Vedatori/SleetClock/Electronics/ESP32 dev board/ESP32 dev board PCB 3D.png

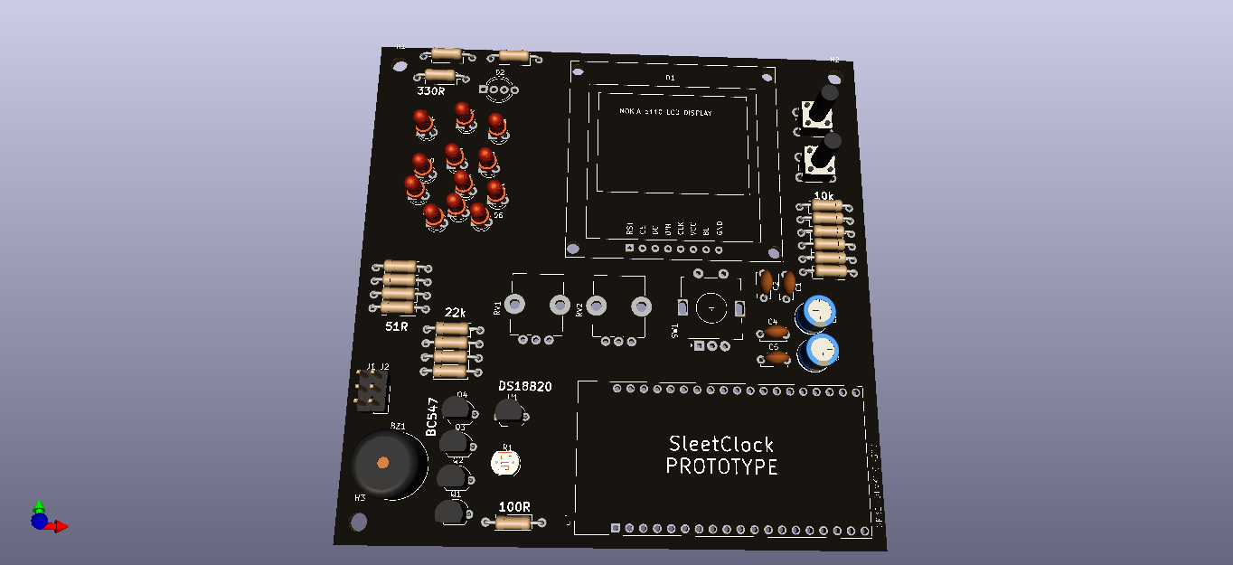
Electronics/ESP32 dev board/ESP32 dev board PCB 3D.png
