Vedatori/SleetClock/Manuals/SupportFiles/034.jpg

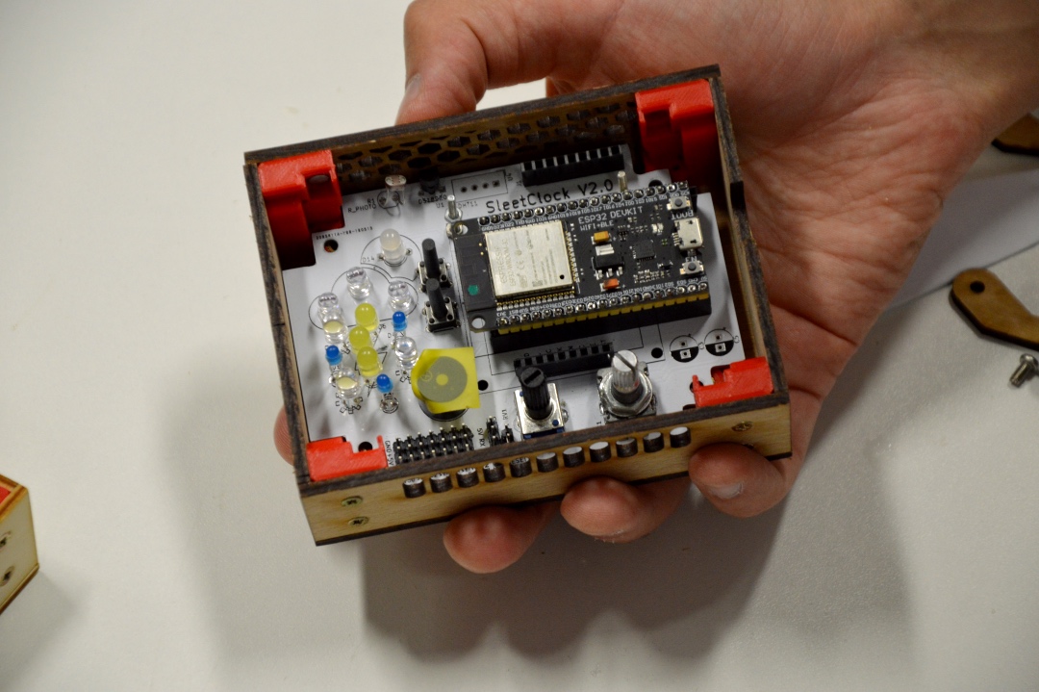
Manuals/SupportFiles/034.jpg
