Vedatori/SleetClock/Manuals/SupportFiles/dsc_0194.jpg

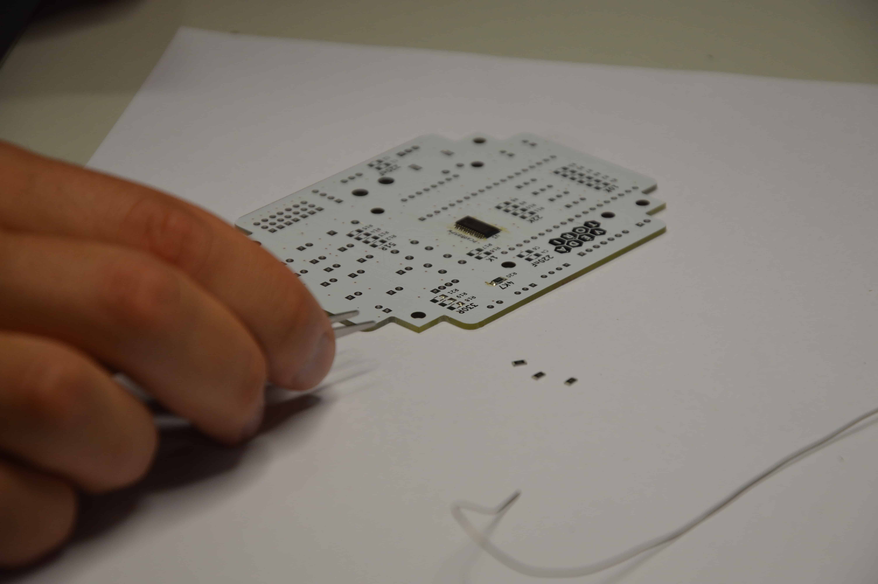
Manuals/SupportFiles/dsc_0194.jpg
