Vedatori/SleetClock/Manuals/SupportFiles/dsc_0197.jpg

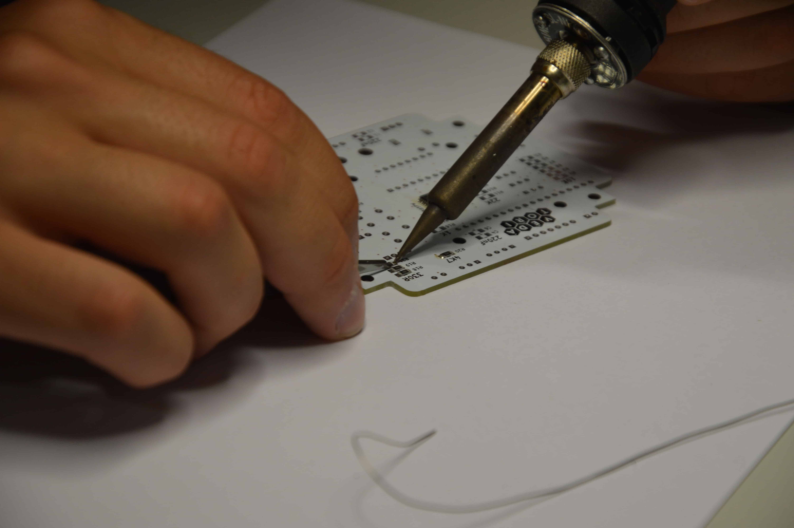
Manuals/SupportFiles/dsc_0197.jpg
