Vedatori/SleetClock/Manuals/SupportFiles/dsc_0290.jpg

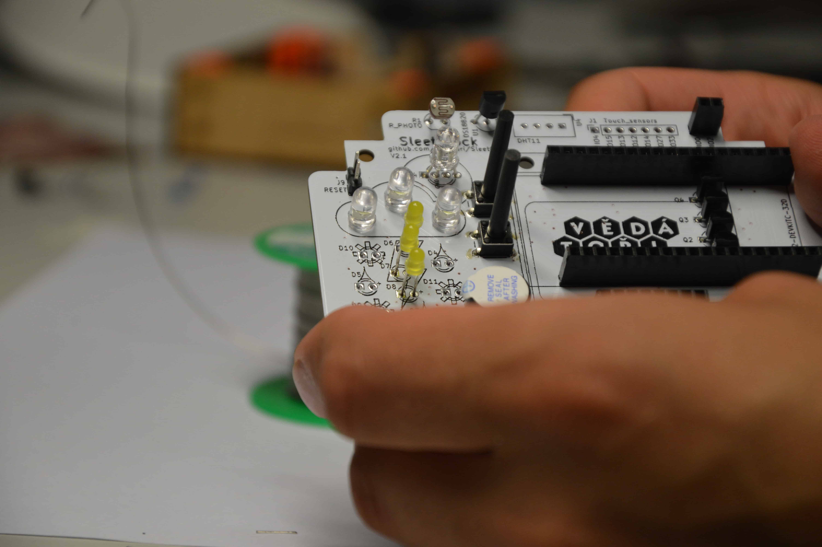
Manuals/SupportFiles/dsc_0290.jpg
