Vedatori/SleetClock/Manuals/SupportFiles/dsc_0303.jpg

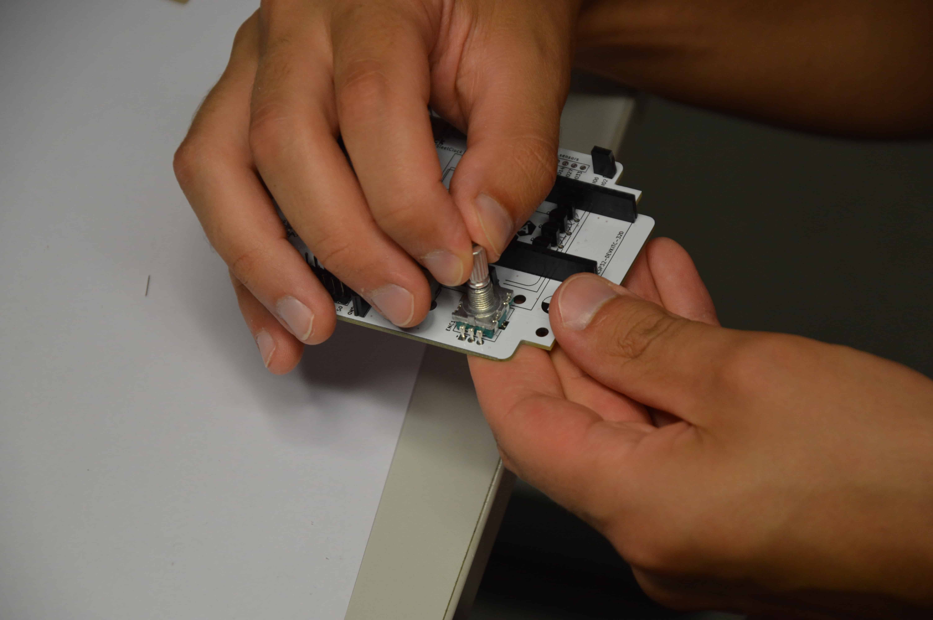
Manuals/SupportFiles/dsc_0303.jpg
