Vedatori/SleetClock/Manuals/SupportFiles/dsc_0311.jpg

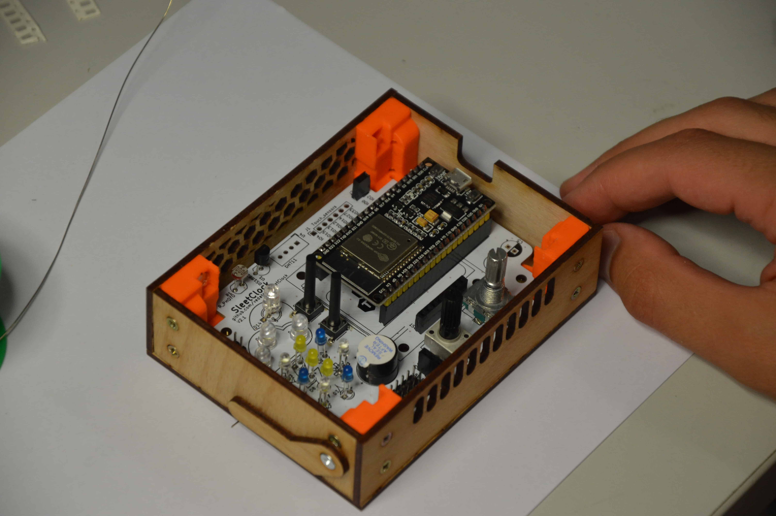
Manuals/SupportFiles/dsc_0311.jpg
