Vedatori/SleetClock/Manuals/SupportFiles/dsc_0338.jpg

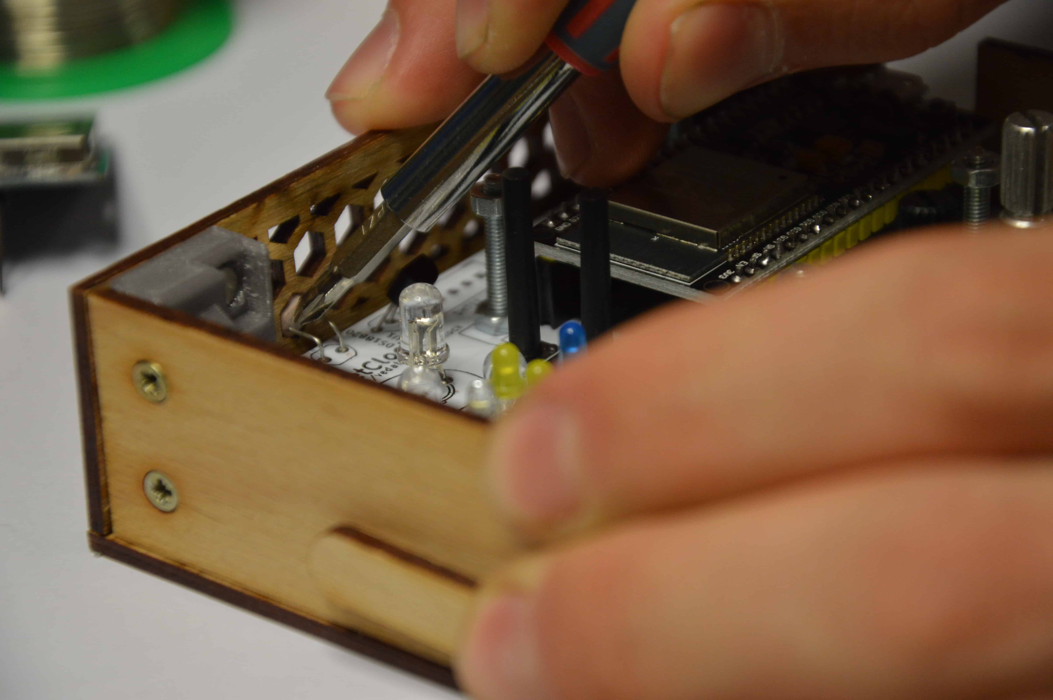
Manuals/SupportFiles/dsc_0338.jpg
